arturo393/Jammer-react/Simulation/Draft1.asc

D1: diode
D2: diode
D3: diode
Q1: npn; 2N3055
Q2: npn
Q3: npn
R1: res; 1k
R2: res; 1kR
R3: res; 22k
R4: res; 20k
R5: res; 1kR
R6: res; 10k
R7: res; 22k
R8: res; 20k
R9: res; 200
R10: res; 200
S1: sw; MYSW
U1: PC817A
U2: PC817A
V1: voltage; PULSE(0 5 1 0 0 2 4 3)
V2: voltage; 5
V3: voltage; PULSE(0 12 1 0 0 2 4 3)
V4: battery; 24
V5: voltage; 5
V6: voltage; PULSE(0 12 1 0 0 2 4 3)
V7: voltage; 5
V8: voltage; PULSE(0 5 1 0 0 2 4 3)
V9: voltage; 12
V10: voltage; 3.3
Named nets: 0
.tran 10
.model MYSW SW(Ron=1 Roff=1Meg Vt=12 Vh=0)
